sixteenmillimeter/GNAL/img/gnal_50ft_v2_spacer.png

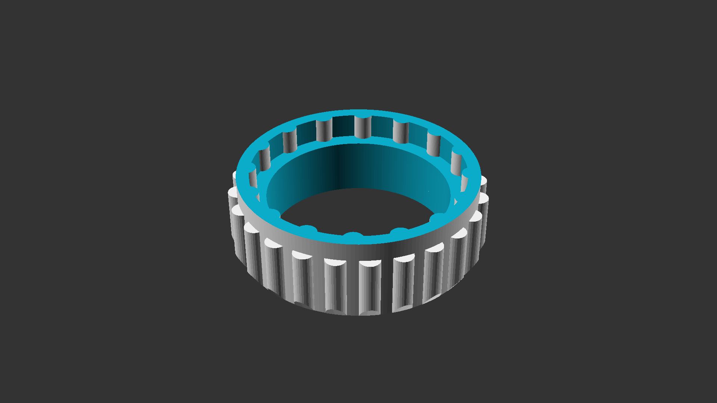
img/gnal_50ft_v2_spacer.png
