sixteenmillimeter/GNAL/img/gnal_50ft_v2_spiral.png

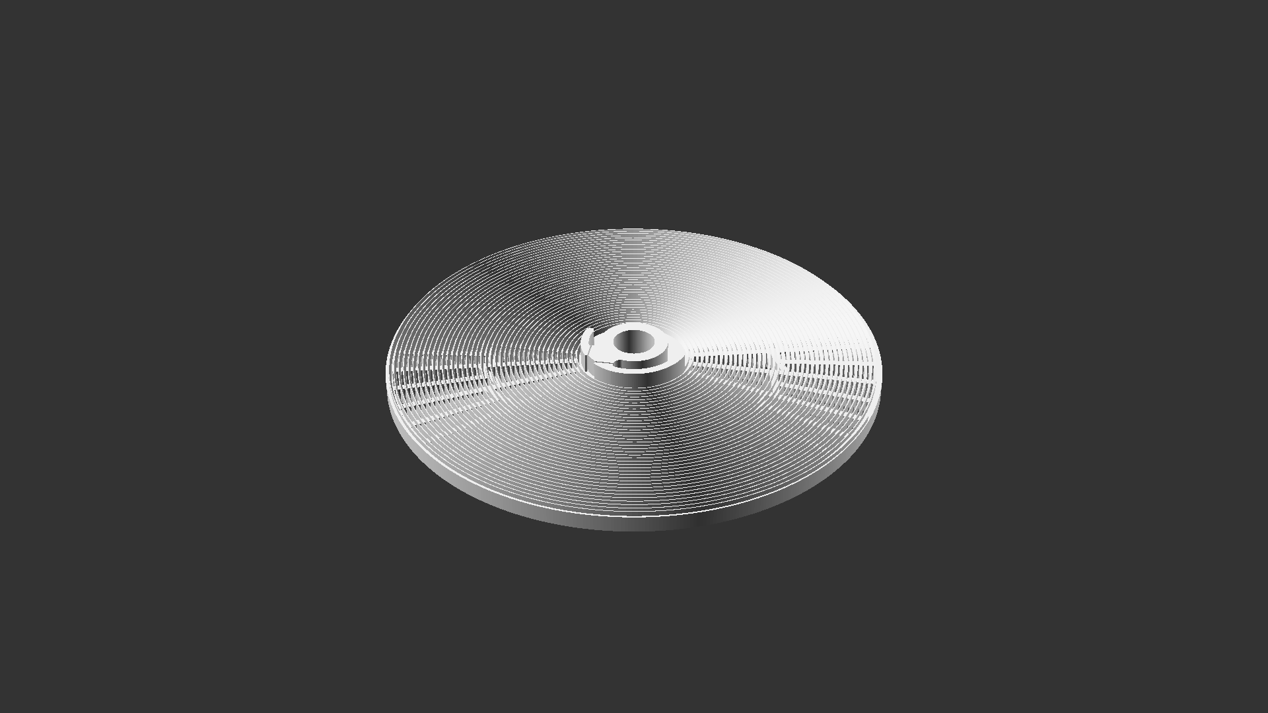
img/gnal_50ft_v2_spiral.png
