sixteenmillimeter/GNAL/img/gnal_50ft_v2_top.png

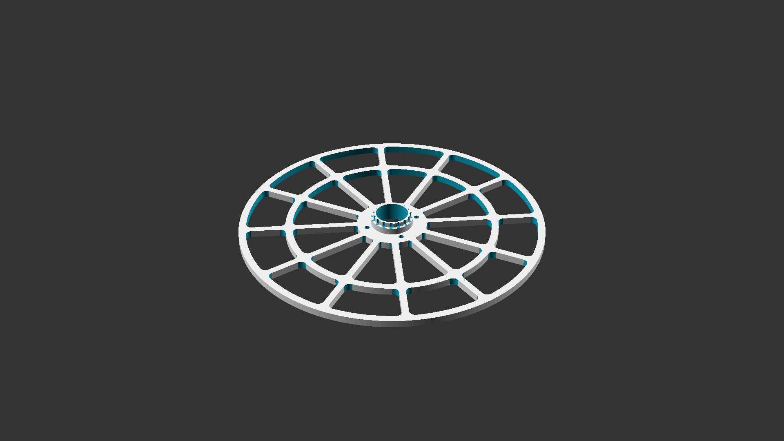
img/gnal_50ft_v2_top.png
