sixteenmillimeter/GNAL/img/gnal_50ft_v3_insert_16.png

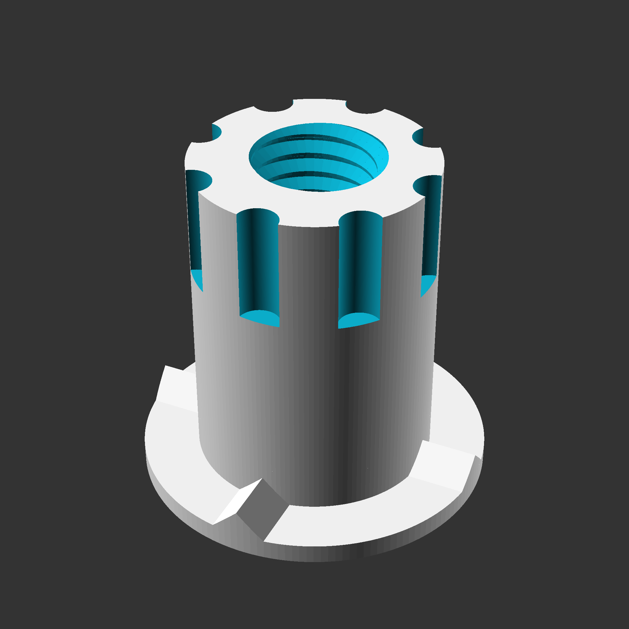
img/gnal_50ft_v3_insert_16.png
