sixteenmillimeter/GNAL/img/gnal_50ft_v3_insert_s8.png

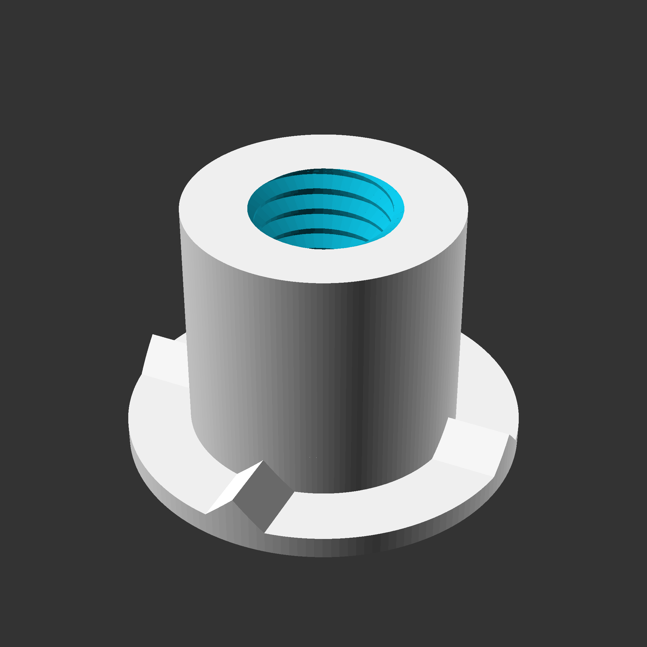
img/gnal_50ft_v3_insert_s8.png
