sixteenmillimeter/GNAL/img/gnal_50ft_v3_spindle_single.png

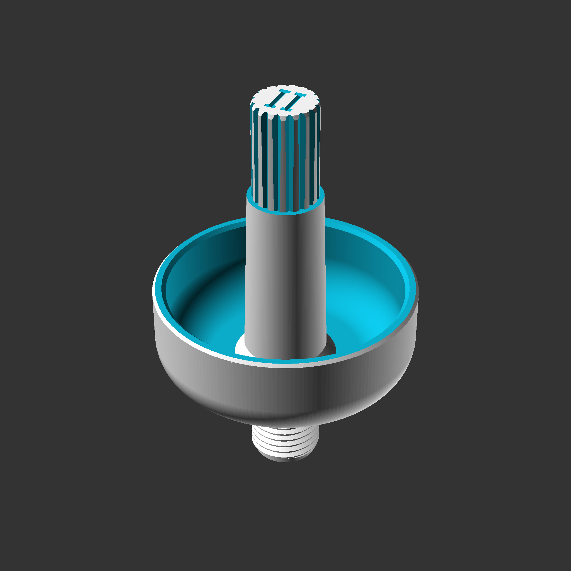
img/gnal_50ft_v3_spindle_single.png
