sixteenmillimeter/GNAL/img/gnal_50ft_v3_spiral.png

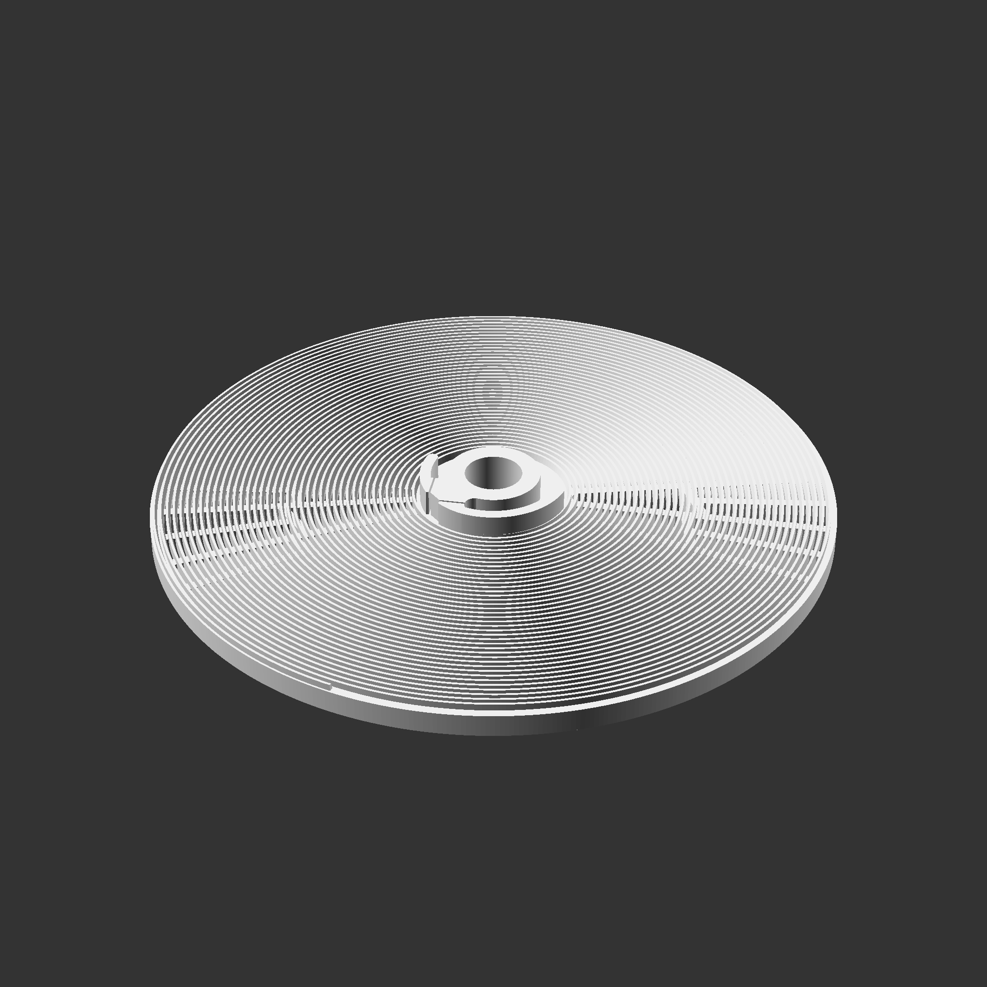
img/gnal_50ft_v3_spiral.png
