sixteenmillimeter/GNAL/img/gnal_50ft_v3_top.png

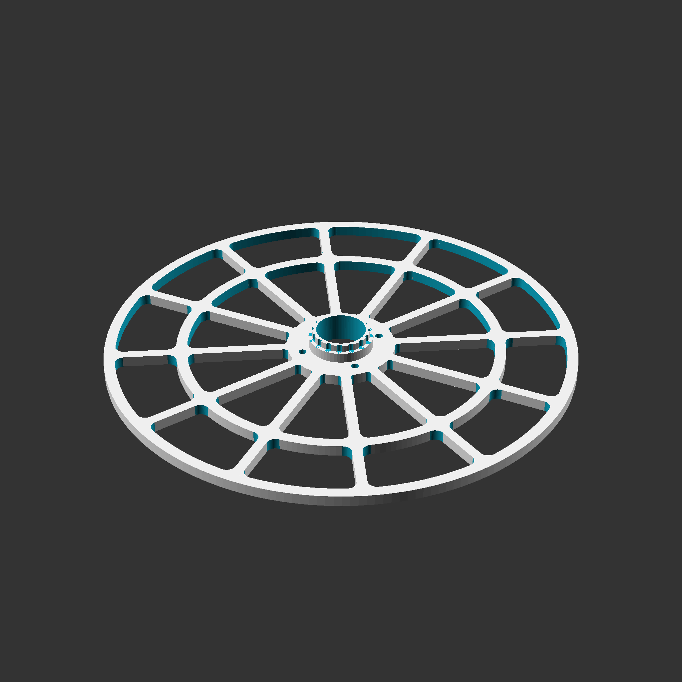
img/gnal_50ft_v3_top.png
