sixteenmillimeter/GNAL/img/gnal_100ft_v3_spindle_single.png

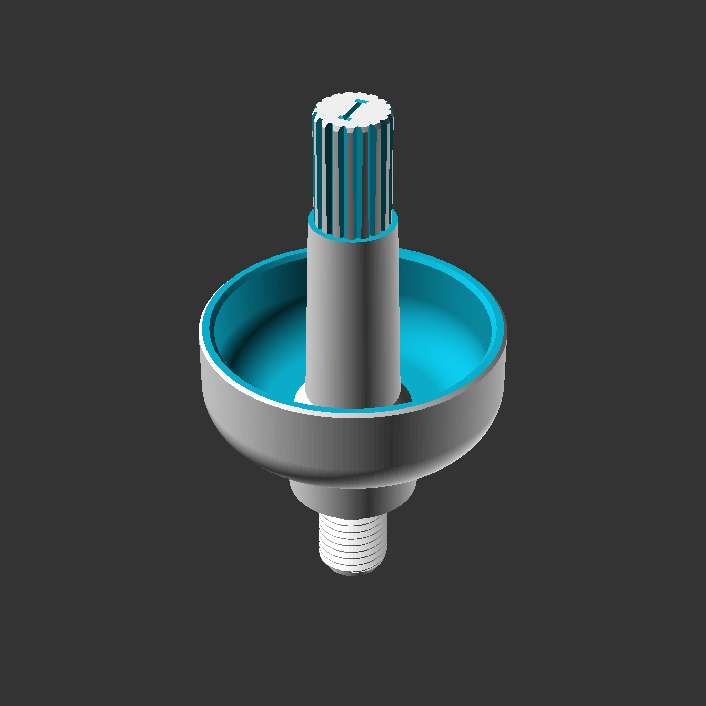
img/gnal_100ft_v3_spindle_single.png
